t-jones14/Arduino-Nextion-PC-System-Control-Panel/Source/Images/bg-cf-sst-pwr-dark.png

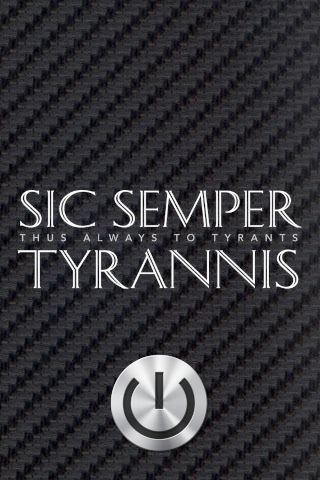
Source/Images/bg-cf-sst-pwr-dark.png
