t-jones14/Arduino-Nextion-PC-System-Control-Panel/Source/Images/carbonFiber-sicSemperTyrannis.png

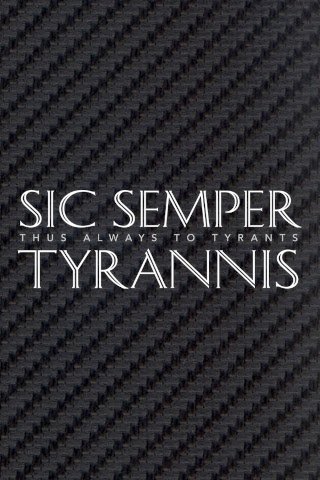
Source/Images/carbonFiber-sicSemperTyrannis.png
