t-jones14/Arduino-Nextion-PC-System-Control-Panel/Source/Images/computer.png

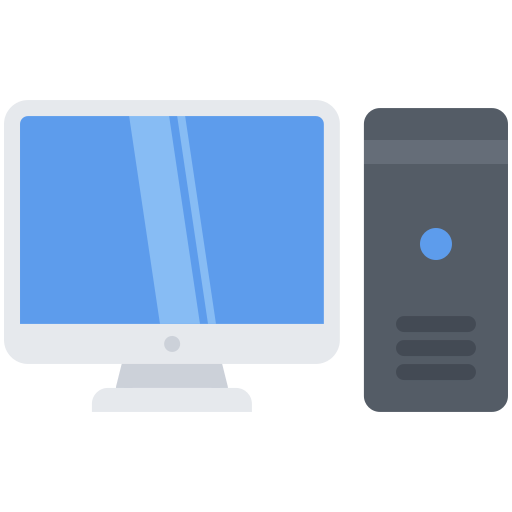
Source/Images/computer.png
