t-jones14/Arduino-Nextion-PC-System-Control-Panel/Source/Images/display-frame.png

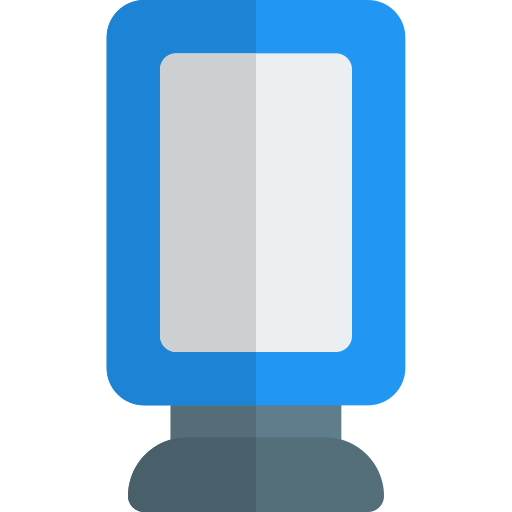
Source/Images/display-frame.png
